miguelr1ce/GDP_12_Quadruped/Morph Designs/Electronics housing/Electronics board DXF.dxf

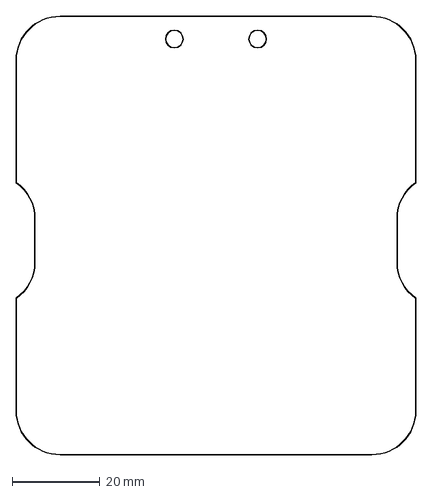
[picture p24: CAD file, 2023-05-07]
Morph Designs/Electronics housing/Electronics board DXF.dxf
91.2 x 100.0 mm
