miguelr1ce/GDP_12_Quadruped/Morph Designs/Gear Assembly/2X Shaft Brace Bearing Mount.stl

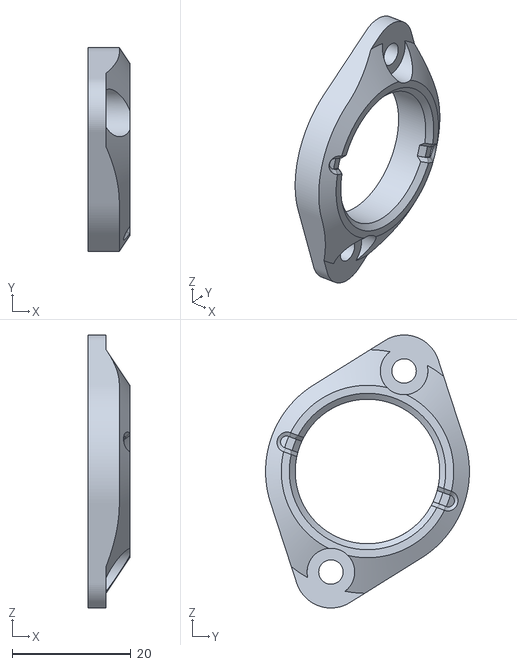
[picture p25: CAD file, 2023-05-07]
Morph Designs/Gear Assembly/2X Shaft Brace Bearing Mount.stl
7.00 x 34.3 x 45.9
