miguelr1ce/GDP_12_Quadruped/Morph Designs/Gear Box Assembly/Back panel.dxf

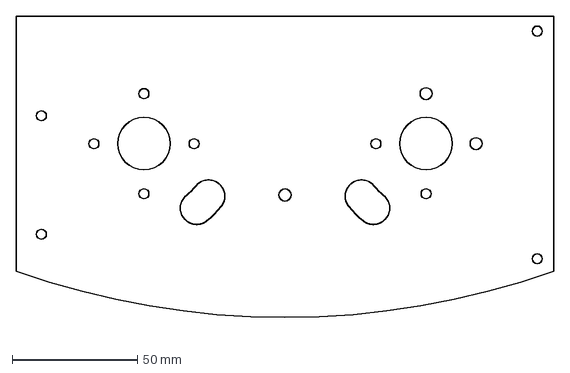
[picture p26: CAD file, 2023-05-07]
Morph Designs/Gear Box Assembly/Back panel.dxf
214.8 x 126.7 mm
