miguelr1ce/GDP_12_Quadruped/Morph Designs/Knee Joint/Gear Holder Inner.stl

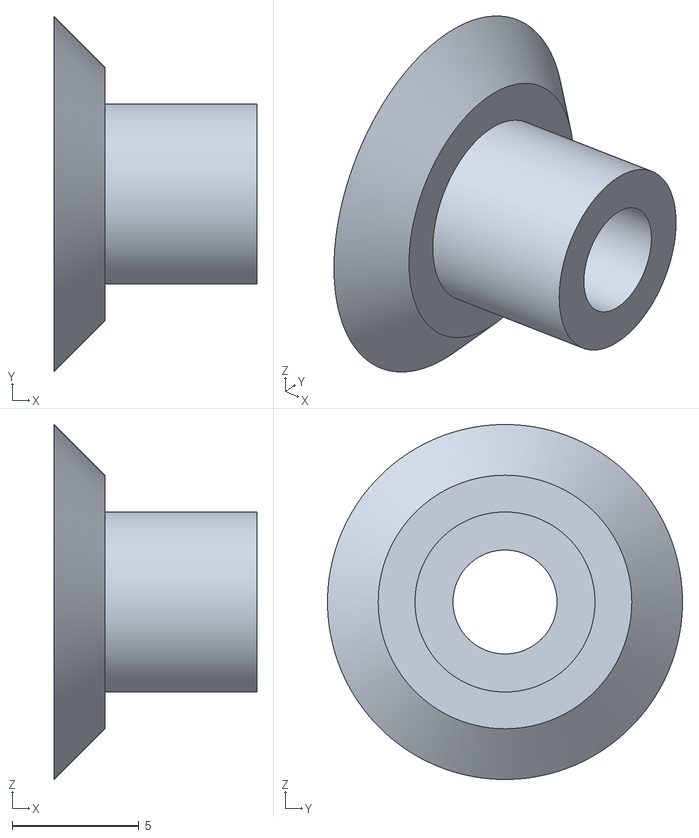
[picture p27: CAD file, 2023-05-07]
Morph Designs/Knee Joint/Gear Holder Inner.stl
8.00 x 14.0 x 14.0
