miguelr1ce/GDP_12_Quadruped/Morph Designs/Legs/Foot Joint 1.stl

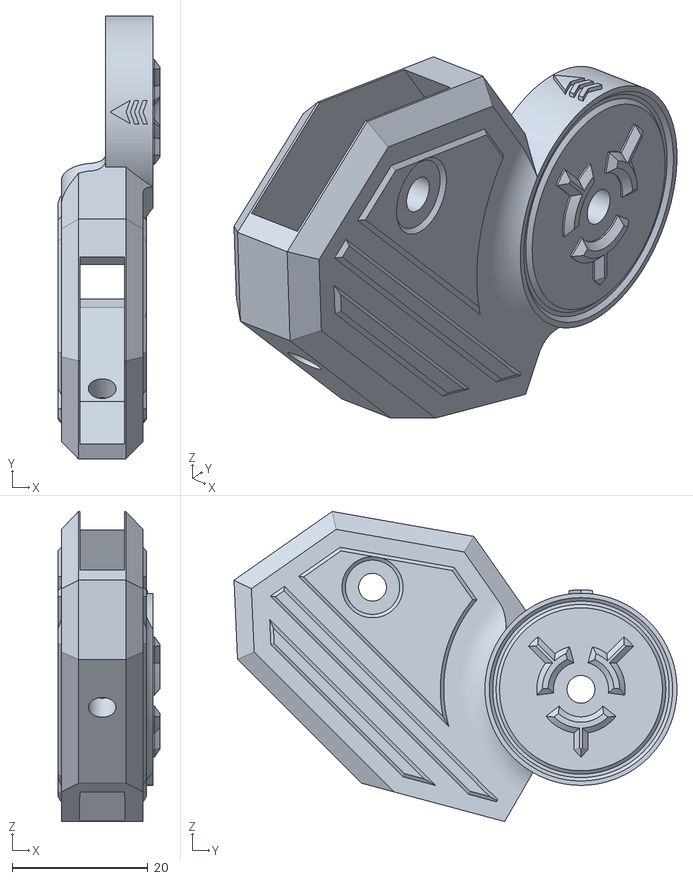
[picture p28: CAD file, 2023-05-07]
Morph Designs/Legs/Foot Joint 1.stl
15.0 x 65.3 x 45.7
