miguelr1ce/GDP_12_Quadruped/Morph Designs/Odrive Mounts/Odrive Mout Acrylic.dxf

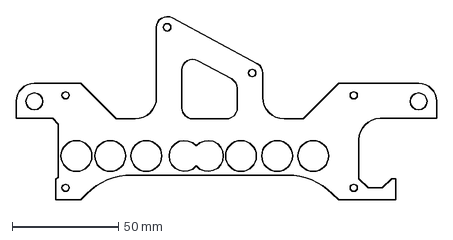
[picture p29: CAD file, 2023-05-07]
Morph Designs/Odrive Mounts/Odrive Mout Acrylic.dxf
197.6 x 86.4 mm
