miguelr1ce/GDP_12_Quadruped/Morph Designs/Worm Gear assembly/Worm Wheel brace.stl

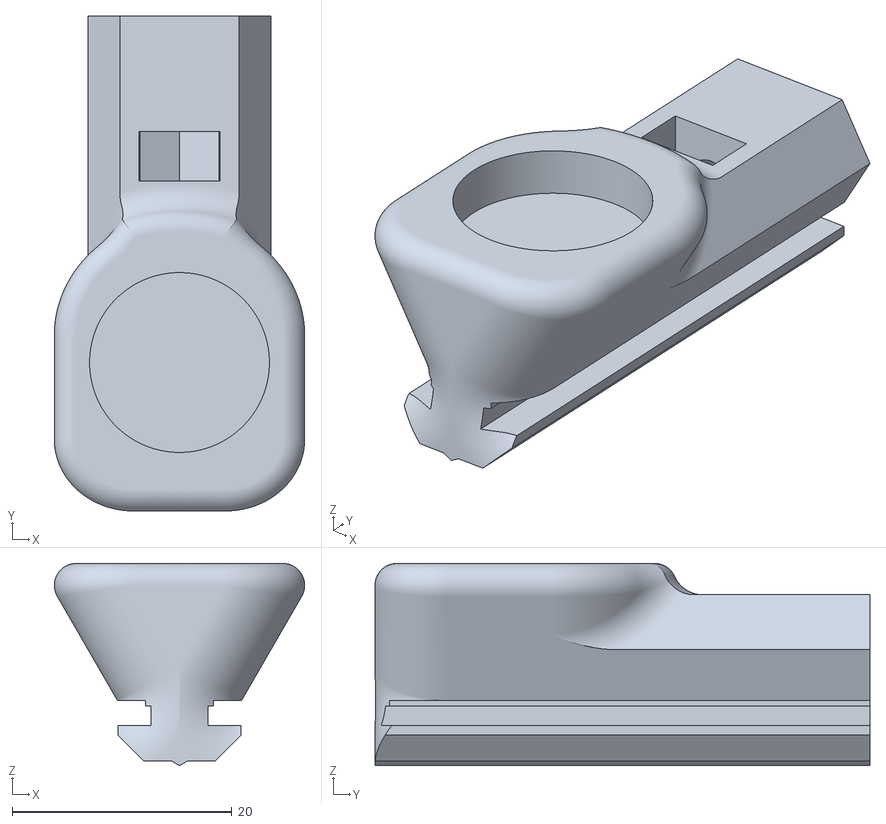
[picture p30: CAD file, 2023-05-07]
Morph Designs/Worm Gear assembly/Worm Wheel brace.stl
22.8 x 45.0 x 18.4
