miguelr1ce/GDP_12_Quadruped/Morph Designs/Body/Aluminium Extrusion Braket.stl

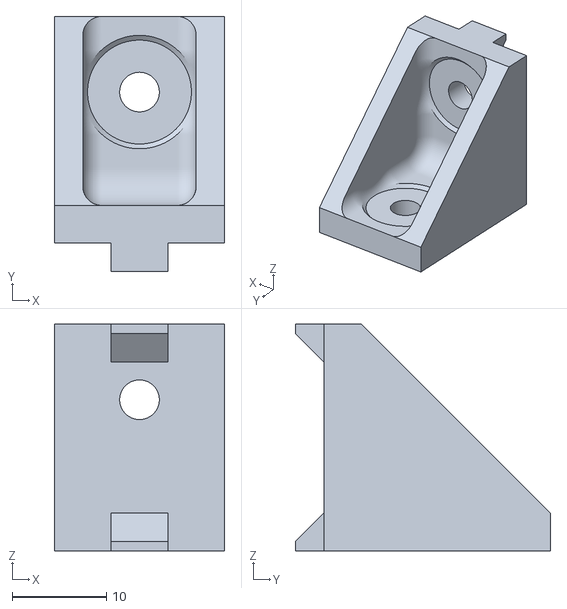
[picture p31: CAD file, 2023-05-07]
Morph Designs/Body/Aluminium Extrusion Braket.stl
18.0 x 27.0 x 24.0
