miguelr1ce/GDP_12_Quadruped/Morph Designs/Gear Assembly/Motor Shaft Mount B.stl

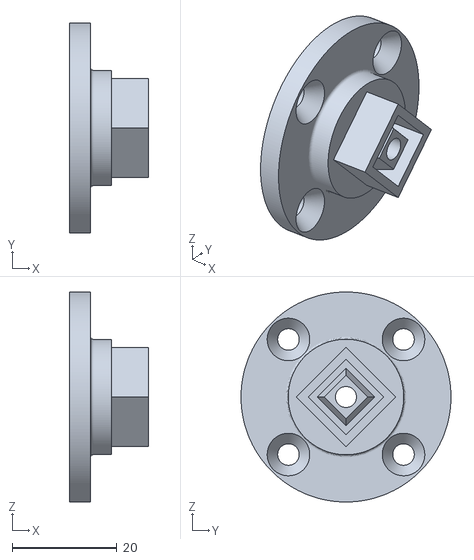
[picture p32: CAD file, 2023-05-07]
Morph Designs/Gear Assembly/Motor Shaft Mount B.stl
15.0 x 40.0 x 40.0
