miguelr1ce/GDP_12_Quadruped/Morph Designs/Gear Box Assembly/Acrylic Mount.stl

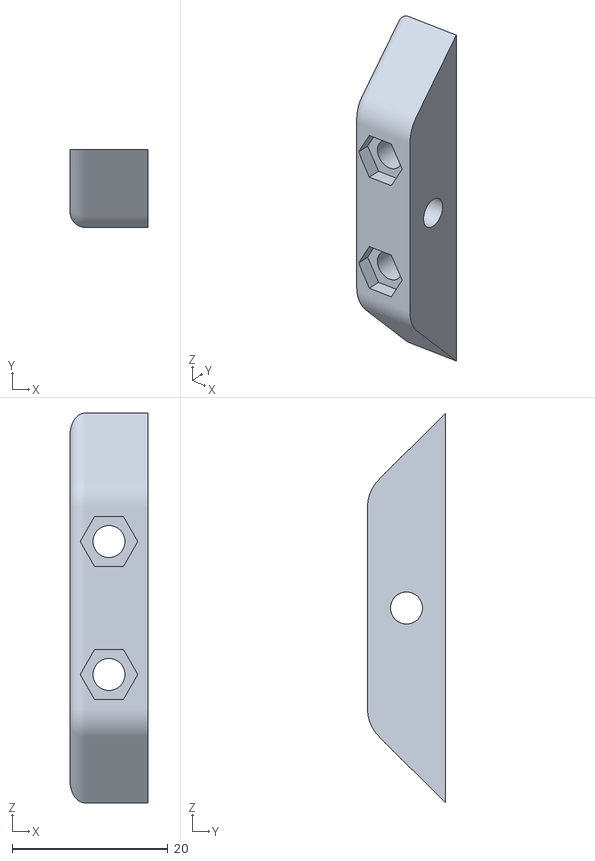
[picture p33: CAD file, 2023-05-07]
Morph Designs/Gear Box Assembly/Acrylic Mount.stl
10.0 x 10.0 x 50.0
