miguelr1ce/GDP_12_Quadruped/Morph Designs/Legs/Thigh Support V2.dxf

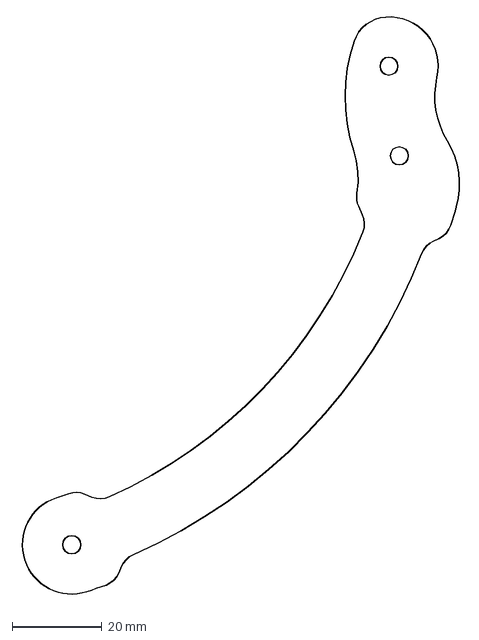
[picture p34: CAD file, 2023-05-07]
Morph Designs/Legs/Thigh Support V2.dxf
99.6 x 130.3 mm
