miguelr1ce/GDP_12_Quadruped/Morph Designs/Odrive Mounts/Odrive Mout Acrylic V2.dxf

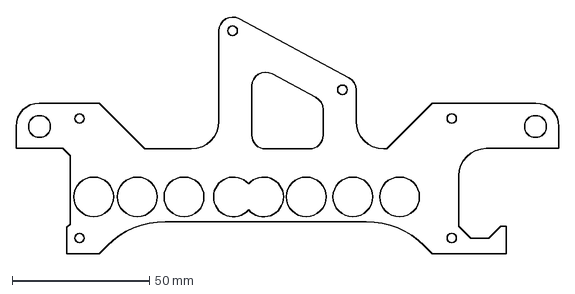
[picture p35: CAD file, 2023-05-07]
Morph Designs/Odrive Mounts/Odrive Mout Acrylic V2.dxf
197.6 x 86.4 mm
