miguelr1ce/GDP_12_Quadruped/Morph Designs/Body/Face Plate Logos.dxf

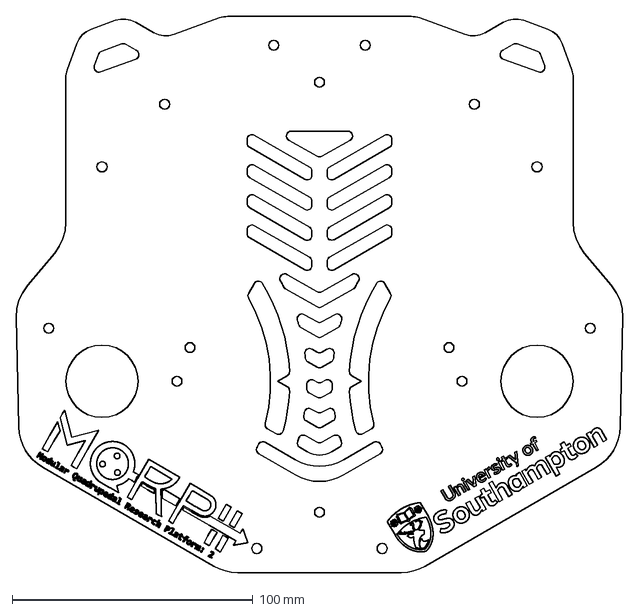
[picture p36: CAD file, 2023-05-07]
Morph Designs/Body/Face Plate Logos.dxf
252.0 x 230.9 mm
