miguelr1ce/GDP_12_Quadruped/Morph Designs/Gear Assembly/Gear Spacer A V2.stl

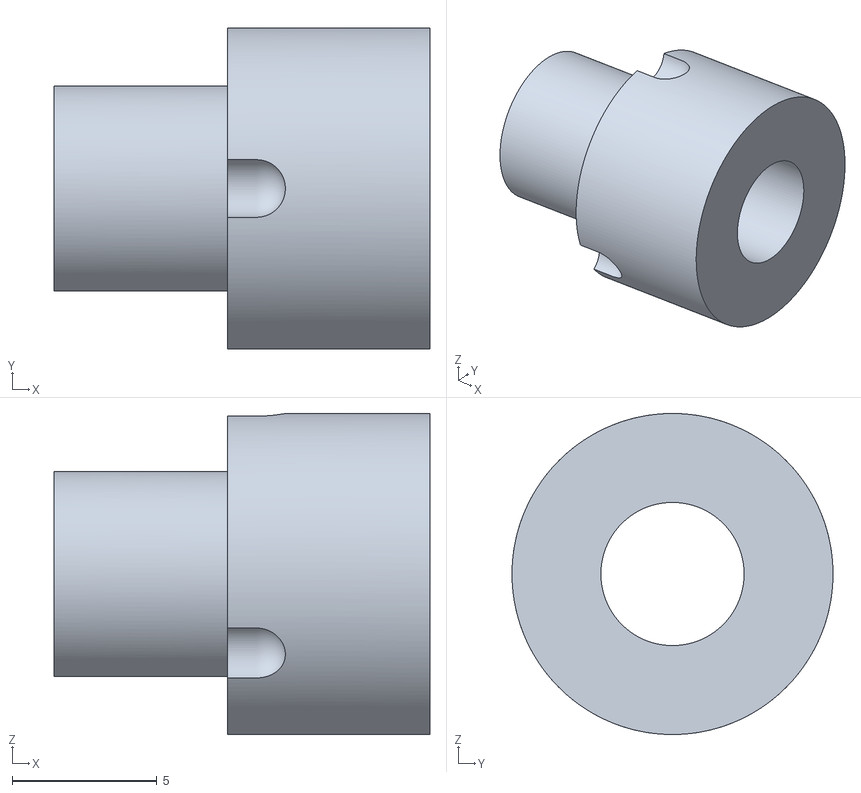
[picture p37: CAD file, 2023-05-07]
Morph Designs/Gear Assembly/Gear Spacer A V2.stl
13.0 x 11.1 x 11.1
