miguelr1ce/GDP_12_Quadruped/Morph Designs/Gear Box Assembly/Pivot attachment.stl

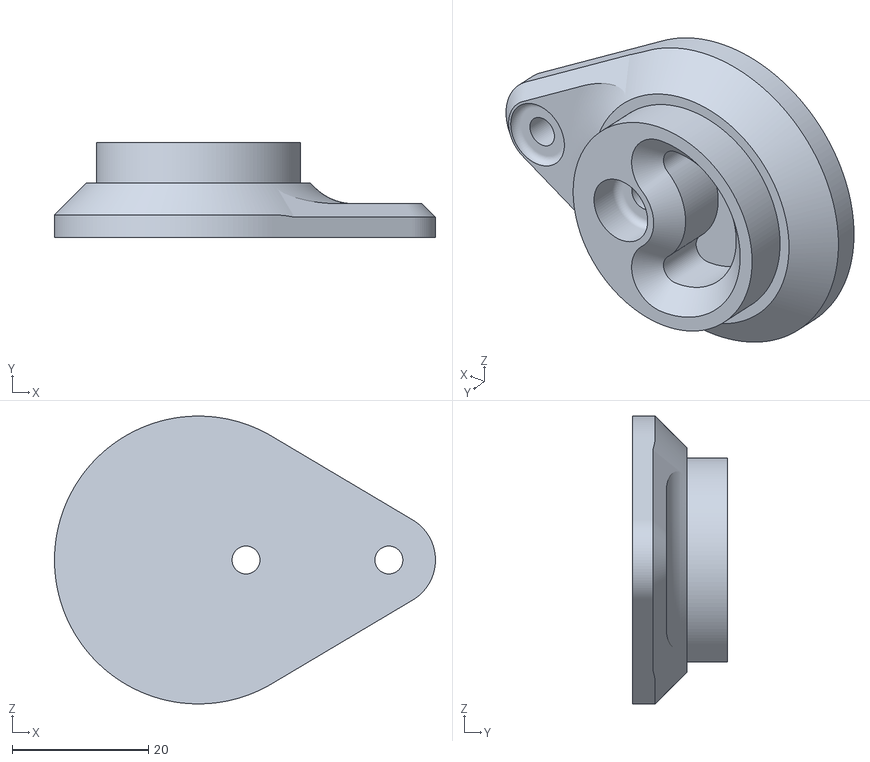
[picture p38: CAD file, 2023-05-07]
Morph Designs/Gear Box Assembly/Pivot attachment.stl
56.0 x 14.0 x 42.3
