miguelr1ce/GDP_12_Quadruped/Morph Designs/Legs/Thigh.dxf

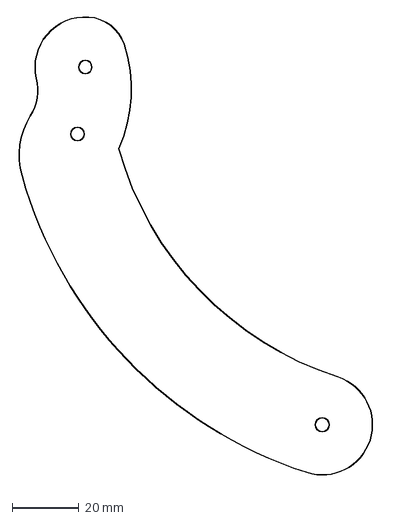
[picture p39: CAD file, 2023-05-07]
Morph Designs/Legs/Thigh.dxf
108.2 x 138.9 mm
