miguelr1ce/GDP_12_Quadruped/Morph Designs/Worm Gear assembly/Motor Shaft Adapter.stl

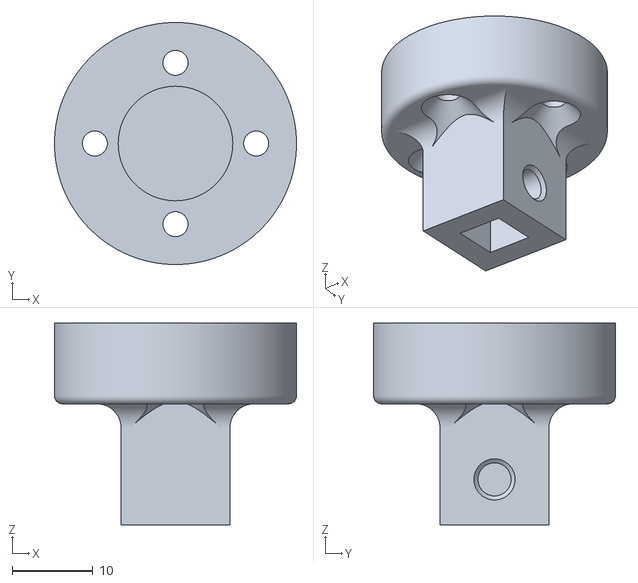
[picture p40: CAD file, 2023-05-07]
Morph Designs/Worm Gear assembly/Motor Shaft Adapter.stl
30.0 x 30.0 x 25.0
