miguelr1ce/GDP_12_Quadruped/Morph Designs/Gear Assembly/Shaft Brace A.stl

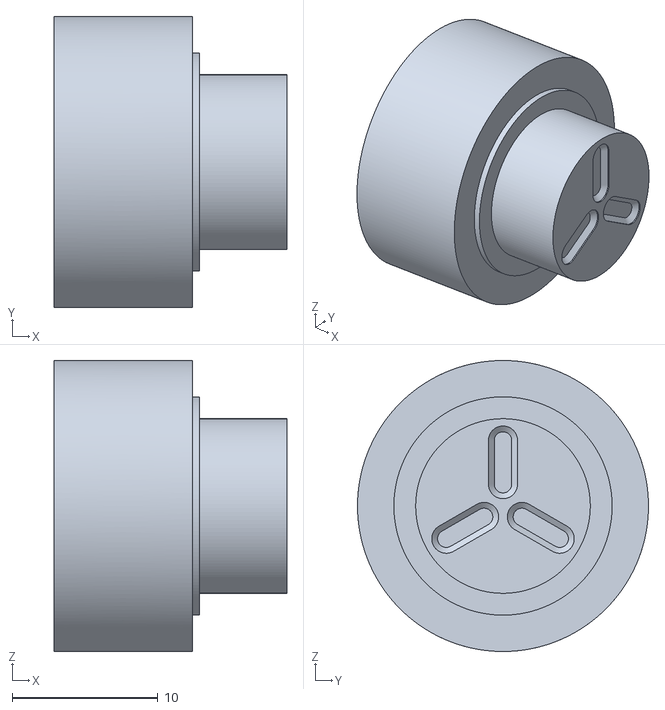
[picture p41: CAD file, 2023-05-07]
Morph Designs/Gear Assembly/Shaft Brace A.stl
16.0 x 20.0 x 20.0
