miguelr1ce/GDP_12_Quadruped/Morph Designs/Gear Box Assembly/Side Plate Mount A.stl

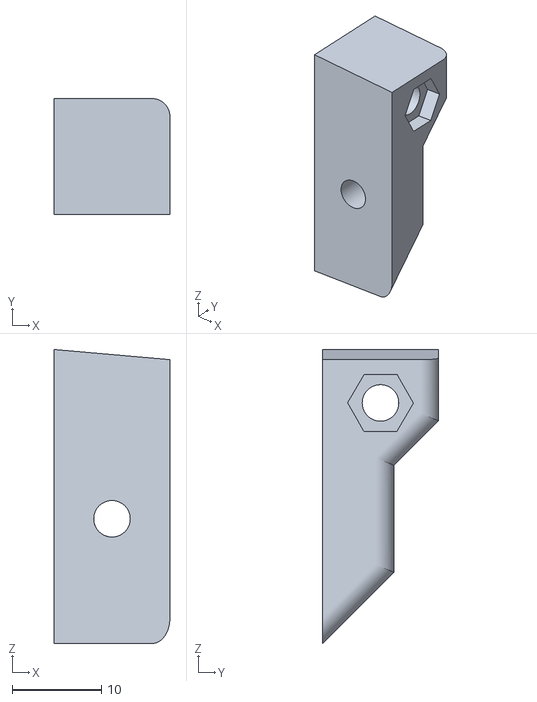
[picture p42: CAD file, 2023-05-07]
Morph Designs/Gear Box Assembly/Side Plate Mount A.stl
13.0 x 13.0 x 33.0
