miguelr1ce/GDP_12_Quadruped/Morph Designs/Legs/Shin.dxf

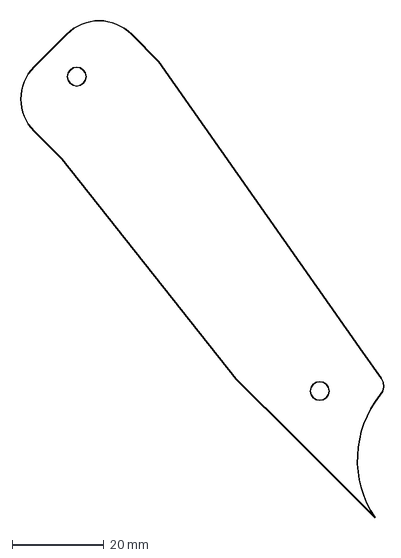
[picture p43: CAD file, 2023-05-07]
Morph Designs/Legs/Shin.dxf
80.3 x 109.4 mm
