miguelr1ce/GDP_12_Quadruped/Morph Designs/Worm Gear assembly/Worm Gear.stl

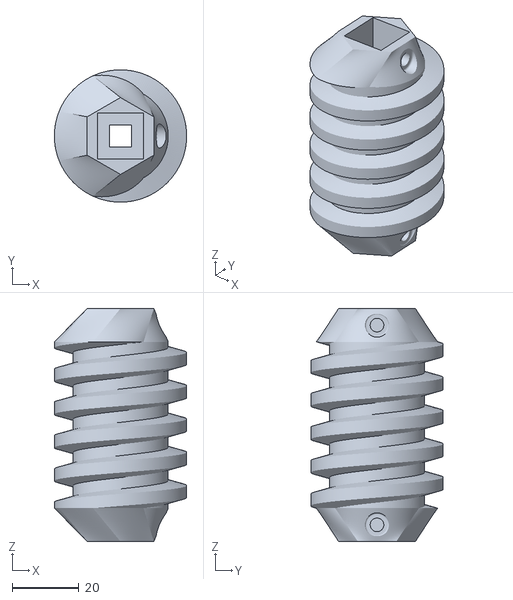
[picture p44: CAD file, 2023-05-07]
Morph Designs/Worm Gear assembly/Worm Gear.stl
39.7 x 39.7 x 70.0
