miguelr1ce/GDP_12_Quadruped/Morph Designs/Gear Assembly/Big Gear.stl

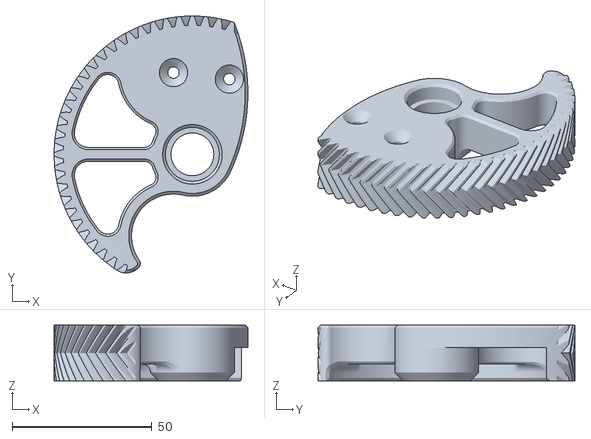
[picture p45: CAD file, 2023-05-07]
Morph Designs/Gear Assembly/Big Gear.stl
69.4 x 92.0 x 20.0
