miguelr1ce/GDP_12_Quadruped/Morph Designs/Gear Box Assembly/Side Plate Mount B.stl

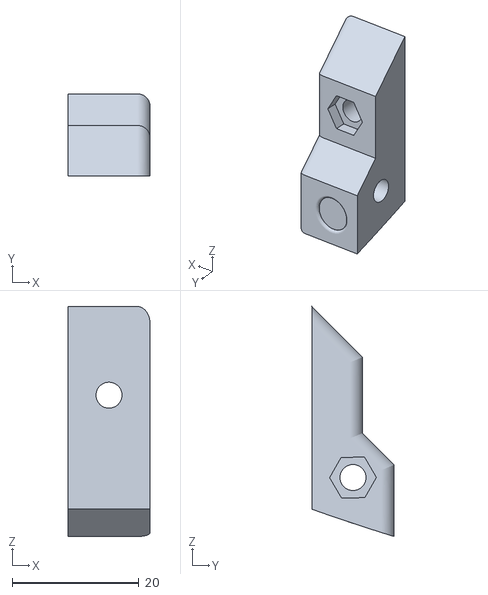
[picture p46: CAD file, 2023-05-07]
Morph Designs/Gear Box Assembly/Side Plate Mount B.stl
13.0 x 13.0 x 36.3
