miguelr1ce/GDP_12_Quadruped/Morph Designs/Legs/Thigh Support.dxf

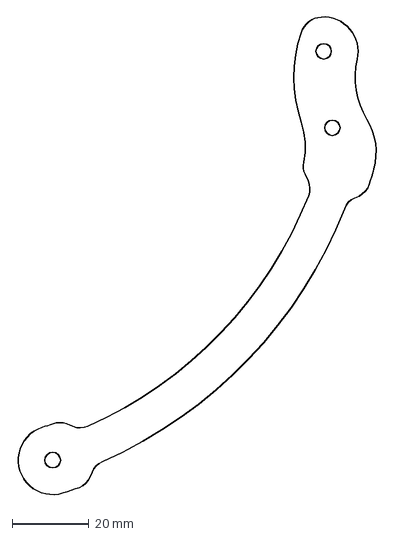
[picture p47: CAD file, 2023-05-07]
Morph Designs/Legs/Thigh Support.dxf
94.6 x 125.5 mm
