miguelr1ce/GDP_12_Quadruped/Morph Designs/Worm Gear assembly/Magnet Mount.stl

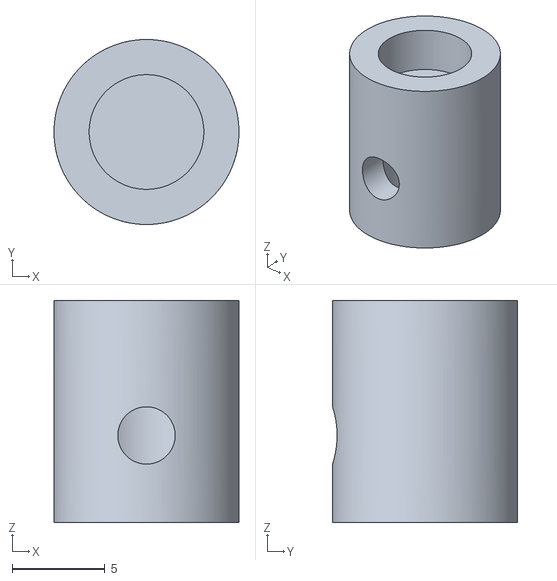
[picture p48: CAD file, 2023-05-07]
Morph Designs/Worm Gear assembly/Magnet Mount.stl
10.00 x 10.0 x 12.0
