miguelr1ce/GDP_12_Quadruped/Morph Designs/Gear Assembly/Gear Spacer B1.stl

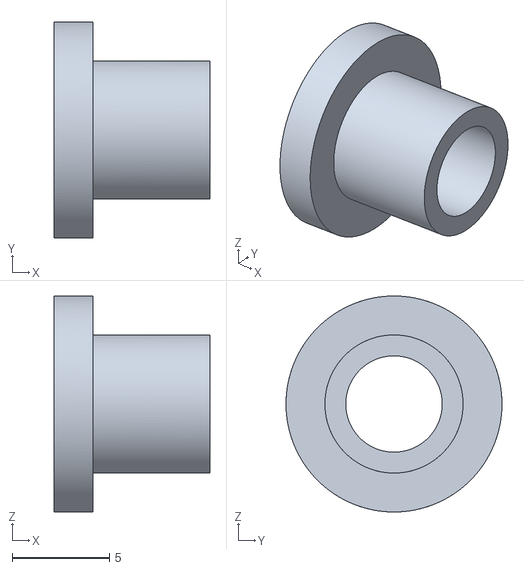
[picture p49: CAD file, 2023-05-07]
Morph Designs/Gear Assembly/Gear Spacer B1.stl
8.00 x 11.1 x 11.1
