miguelr1ce/GDP_12_Quadruped/Morph Designs/Gear Box Assembly/Large Motor Encoder Mount.stl

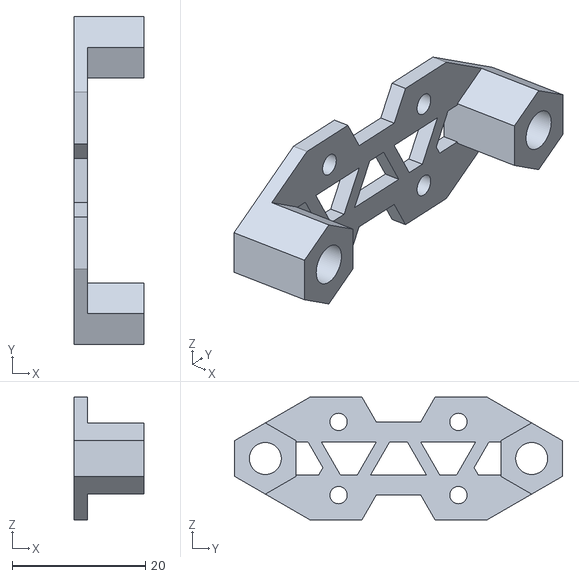
[picture p50: CAD file, 2023-05-07]
Morph Designs/Gear Box Assembly/Large Motor Encoder Mount.stl
10.5 x 49.3 x 18.5
