miguelr1ce/GDP_12_Quadruped/Morph Designs/Worm Gear assembly/Motor and encoder Mount.stl

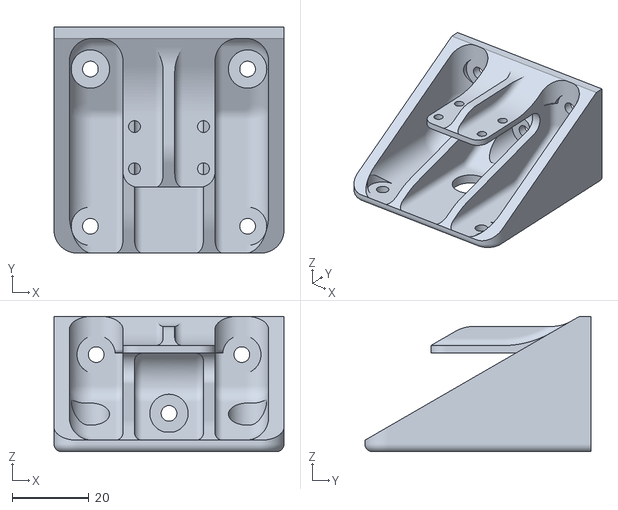
[picture p51: CAD file, 2023-05-07]
Morph Designs/Worm Gear assembly/Motor and encoder Mount.stl
60.0 x 59.0 x 35.3
