miguelr1ce/GDP_12_Quadruped/Morph Designs/Gear Assembly/Gear Spacer C.stl

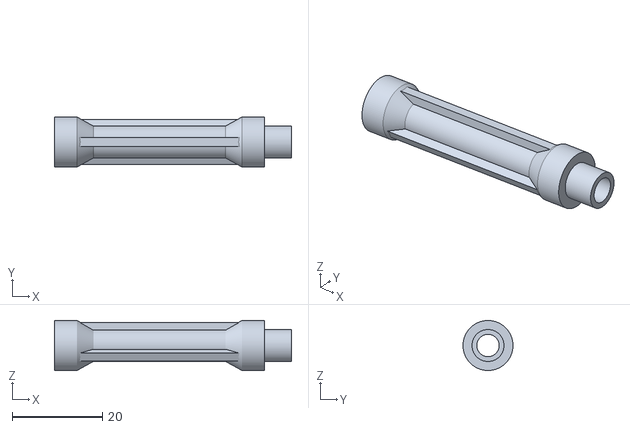
[picture p52: CAD file, 2023-05-07]
Morph Designs/Gear Assembly/Gear Spacer C.stl
52.6 x 11.1 x 11.1
