miguelr1ce/GDP_12_Quadruped/Morph Designs/Gear Box Assembly/Acrylic plate.dxf

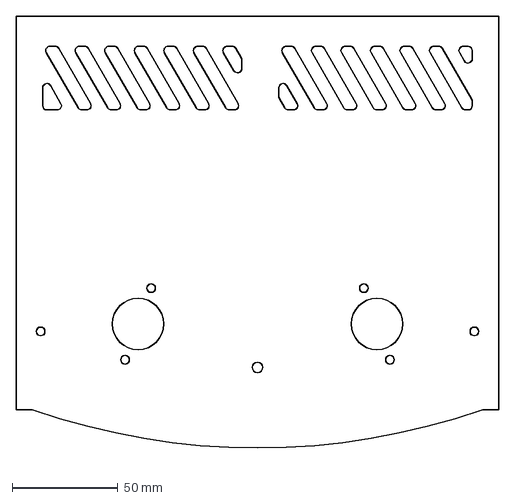
[picture p53: CAD file, 2023-05-07]
Morph Designs/Gear Box Assembly/Acrylic plate.dxf
227.8 x 209.8 mm
