miguelr1ce/GDP_12_Quadruped/Morph Designs/Gear Box Assembly/Bearing Clasp Top.stl

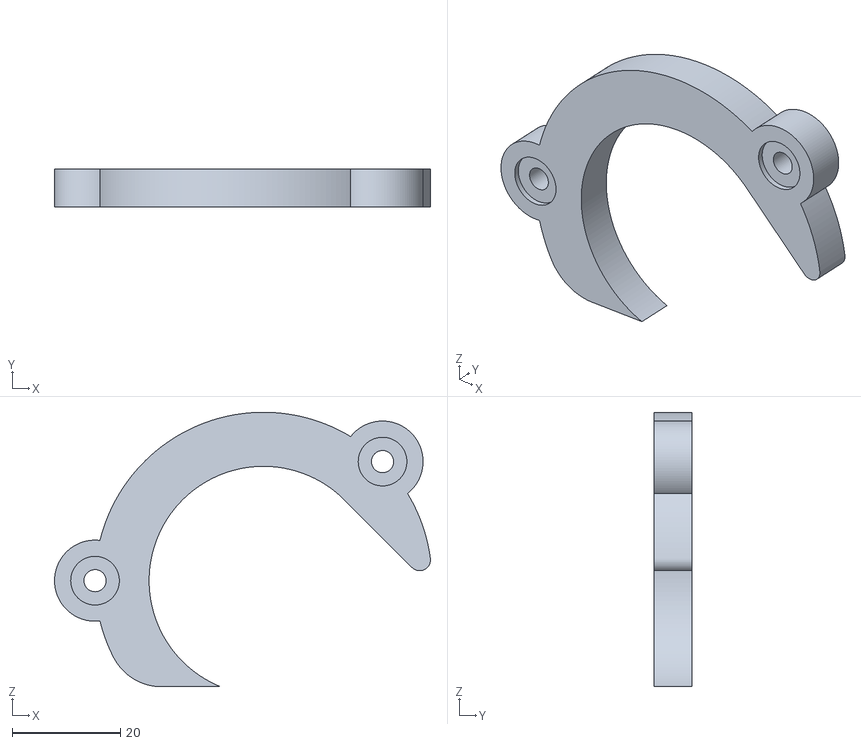
[picture p54: CAD file, 2023-05-07]
Morph Designs/Gear Box Assembly/Bearing Clasp Top.stl
69.5 x 7.00 x 50.8
