miguelr1ce/GDP_12_Quadruped/Morph Designs/Gear Assembly/Motor Shaft Mount A.stl

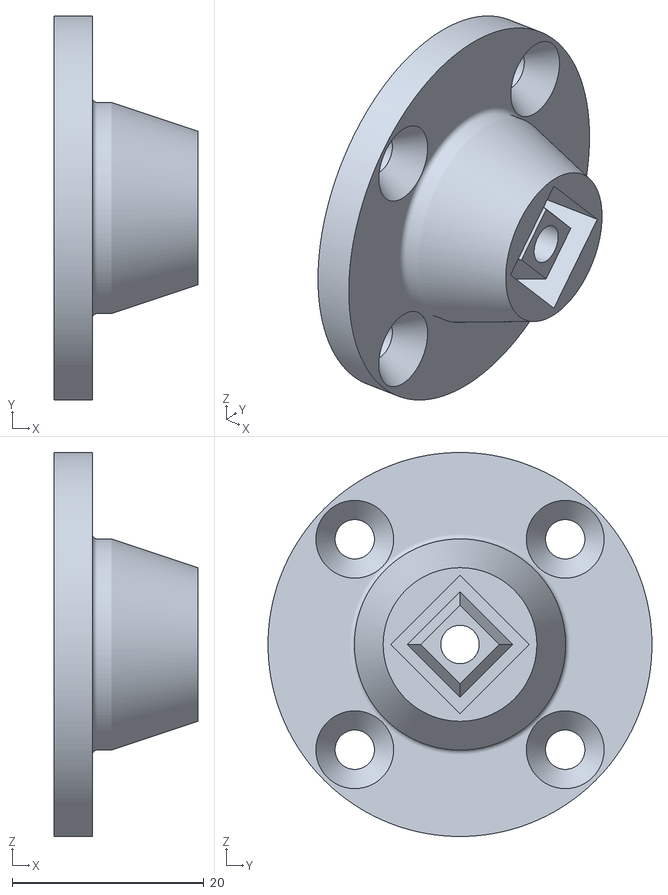
[picture p55: CAD file, 2023-05-07]
Morph Designs/Gear Assembly/Motor Shaft Mount A.stl
15.0 x 40.0 x 40.0
