miguelr1ce/GDP_12_Quadruped/Morph Designs/Gear Box Assembly/Bearing clasp Bottom.stl

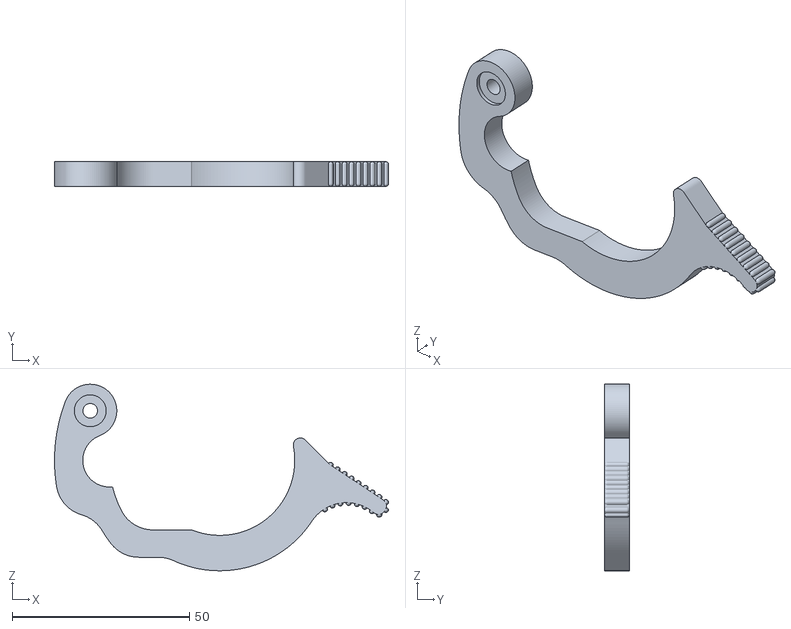
[picture p56: CAD file, 2023-05-07]
Morph Designs/Gear Box Assembly/Bearing clasp Bottom.stl
94.2 x 7.00 x 52.6
