miguelr1ce/GDP_12_Quadruped/Morph Designs/Gear Box Assembly/Side Panel A.dxf

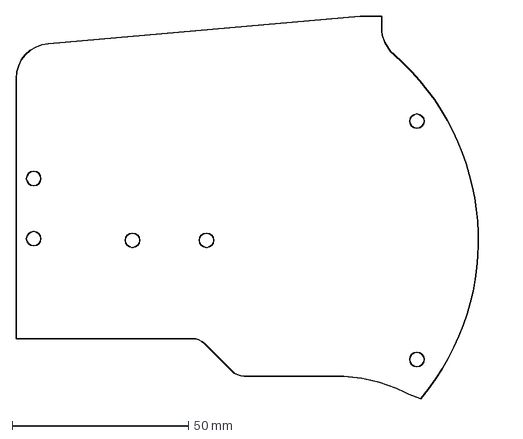
[picture p57: CAD file, 2023-05-07]
Morph Designs/Gear Box Assembly/Side Panel A.dxf
139.1 x 108.4 mm
