miguelr1ce/GDP_12_Quadruped/Final_Code_Draft/structdef.h

#ifndef STRUCTDEF_H
#define STRUCTDEF_H

#define legn 4 //number of legs
#define coor 3 //x,y,z
#define itr 8 //number of iterations
#define timer 500

//Structure Definition
struct gait_struct{
  double March[itr][legn][coor]={{{0, 0, 0}, {0, 0, 0}, {0, 0, 0}, {0, 0, 0}}, {{0, 0, 50.0}, {0, 0, 0}, {0, 0, 0}, {0, 0, 0}}, {{0, 0, 0}, {0, 0, 0}, {0, 0, 0}, {0, 0, 0}}, {{0, 0, 0}, {0, 0, 50.0}, {0, 0, 0}, {0, 0, 0}}, {{0, 0, 0}, {0, 0, 0}, {0, 0, 0}, {0, 0, 0}}, {{0, 0, 0}, {0, 0, 0}, {0, 0, 50.0}, {0, 0, 0}}, {{0, 0, 0}, {0, 0, 0}, {0, 0, 0}, {0, 0, 0}}, {{0, 0, 0}, {0, 0, 0}, {0, 0, 0}, {0, 0, 50.0}}} ;
  double FB[itr][legn][coor]={{{0, -60, 0}, {0, -20, 0}, {0, 20, 0}, {0, 60, 0}}, {{0, 0, 0}, {0, -40, 0}, {0, 0, 0}, {0, 40, 0}}, {{0, 60, 0}, {0, -60, 0}, {0, -20, 0}, {0, 20, 0}}, {{0, 40, 0}, {0, 0, 0}, {0, -40, 0}, {0, 0, 0}}, {{0, 20, 0}, {0, 60, 0}, {0, -60, 0}, {0, -20, 0}}, {{0, 0, 0}, {0, 40, 0}, {0, 0, 0}, {0, -40, 0}}, {{0, -20, 0}, {0, 20, 0}, {0, 60, 0}, {0, -60, 0}}, {{0, -40, 0}, {0, 0, 0}, {0, 40, 0}, {0, 0, 0}}};
  double LR[itr][legn][coor]={{{-60, 0, 0}, {-20, 0, 0}, {20, 0, 0}, {60, 0, 0}}, {{0, 0, 0}, {-40, 0, 0}, {0, 0, 0}, {40, 0, 0}}, {{60, 0, 0}, {-60, 0, 0}, {-20, 0, 0}, {20, 0, 0}}, {{40, 0, 0}, {0, 0, 0}, {-40, 0, 0}, {0, 0, 0}}, {{20, 0, 0}, {60, 0, 0}, {-60, 0, 0}, {-20, 0, 0}}, {{0, 0, 0}, {40, 0, 0}, {0, 0, 0}, {-40, 0, 0}}, {{-20, 0, 0}, {20, 0, 0}, {60, 0, 0}, {-60, 0, 0}}, {{-40, 0, 0}, {0, 0, 0}, {40, 0, 0}, {0, 0, 0}}} ;
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
};

struct STRUCT { //defining struct called test_packet
  float item1;  // LR
  float item2;  // FB
  float item3;
  float item4;
  int item5;
  int item6;
  int item7;
  int item8;
  int item9;
  int item10;
} packet;

#endif
